hlord2000/nordic-lib-kicad/blocks/nRF54L.kicad_blocks/nRF54L15-CAXX_Reference_Design.kicad_block/nRF54L15-CAXX_Reference_Design.kicad_sch

## KiCad design blocks/nRF54L.kicad_blocks/nRF54L15-CAXX_Reference_Design.kicad_block/nRF54L15-CAXX_Reference_Design.kicad_sch (2026-04-14)

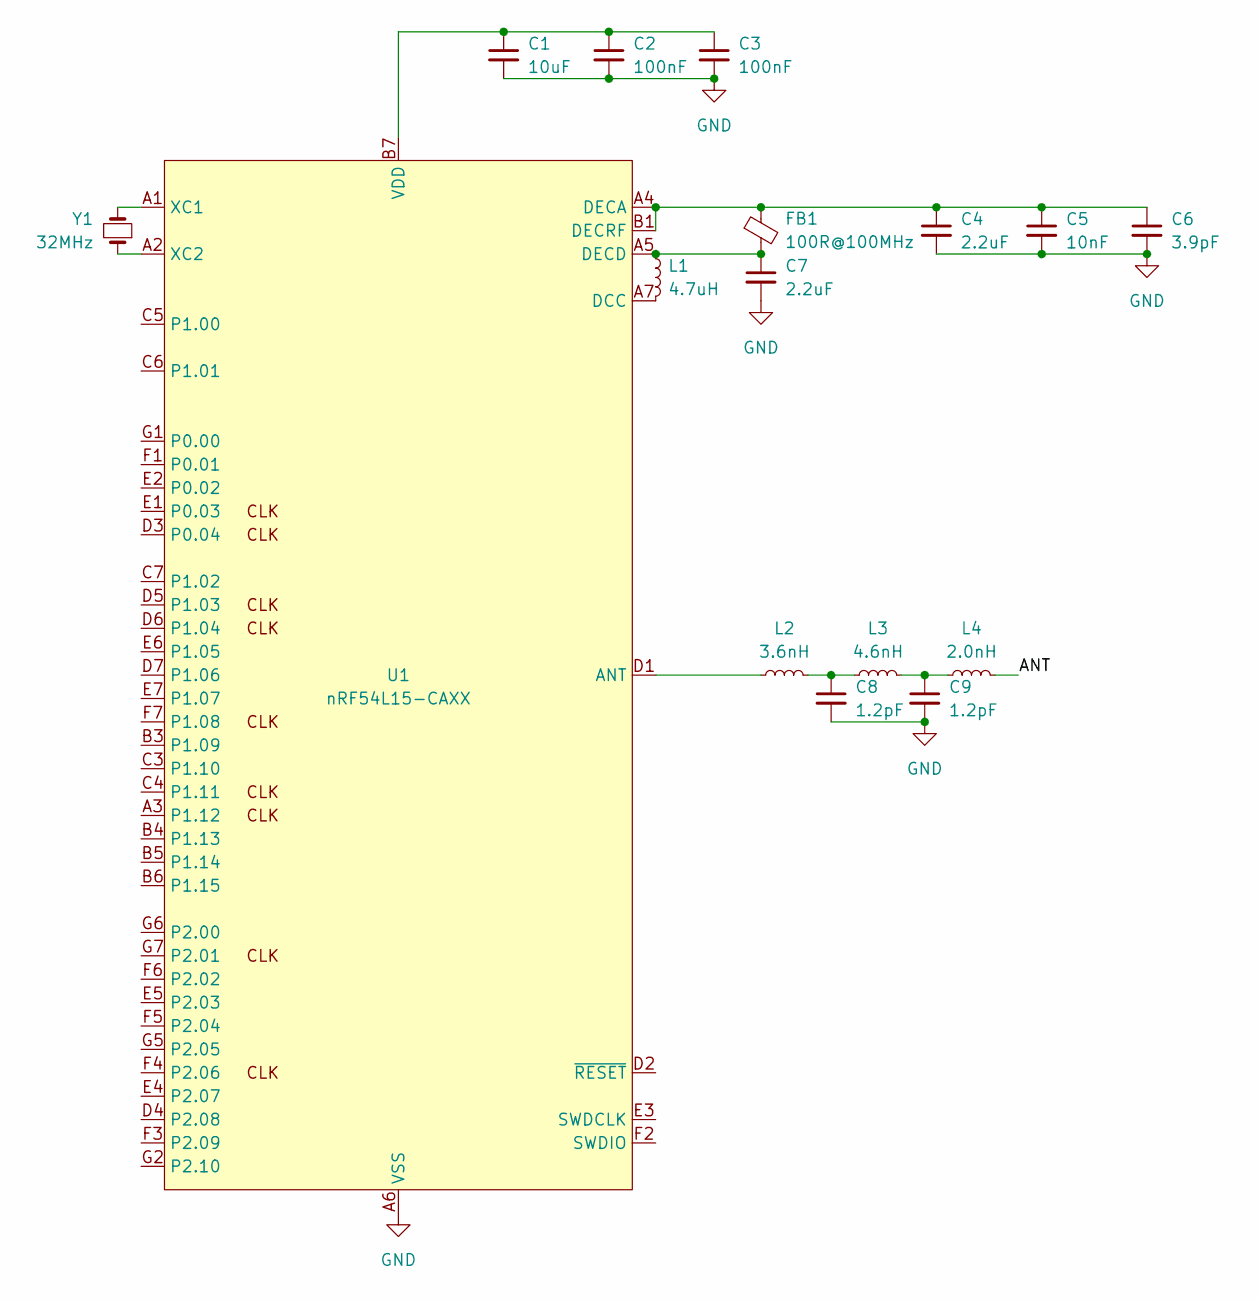
[picture p3: schematic nRF54L15-CAXX_Reference_Design.kicad_sch]

Parts:
C1: 10uF
C2, C3: 100nF
C4, C7: 2.2uF
C5: 10nF
C6: 3.9pF
C8, C9: 1.2pF
FB1: 100R@100MHz
L1: 4.7uH
L2: 3.6nH
L3: 4.6nH
L4: 2.0nH
U1: nRF54L15-CAXX; BGA-47_7x7_2.451x2.245mm
Y1: 32MHz

Connections:
ANT: L4.2
GND: C1.2, C2.2, C3.2, C4.2, C5.2, C6.2, C7.2, C8.2, C9.2, U1.A6 (VSS), U1.C2 (VSS_PA), U1.G4 (VSS)
unnamed: C1.1, C2.1, C3.1, U1.B7 (VDD), U1.G3 (VDD)
unnamed: C4.1, C5.1, C6.1, FB1.1, U1.A4 (DECA), U1.B1 (DECRF)
unnamed: C7.1, FB1.2, L1.1, U1.A5 (DECD)
unnamed: C8.1, L2.2, L3.1
unnamed: C9.1, L3.2, L4.1
unnamed: L1.2, U1.A7 (DCC)
unnamed: L2.1, U1.D1 (ANT)
unnamed: U1.A1 (XC1), Y1.2
unnamed: U1.A2 (XC2), Y1.1
