hlord2000/nordic-lib-kicad/blocks/nRF54L.kicad_blocks/nRF54LM20A-PAXX_Reference_Design.kicad_block/nRF54LM20A-PAXX_Reference_Design.kicad_sch

## KiCad design blocks/nRF54L.kicad_blocks/nRF54LM20A-PAXX_Reference_Design.kicad_block/nRF54LM20A-PAXX_Reference_Design.kicad_sch (2025-09-18)

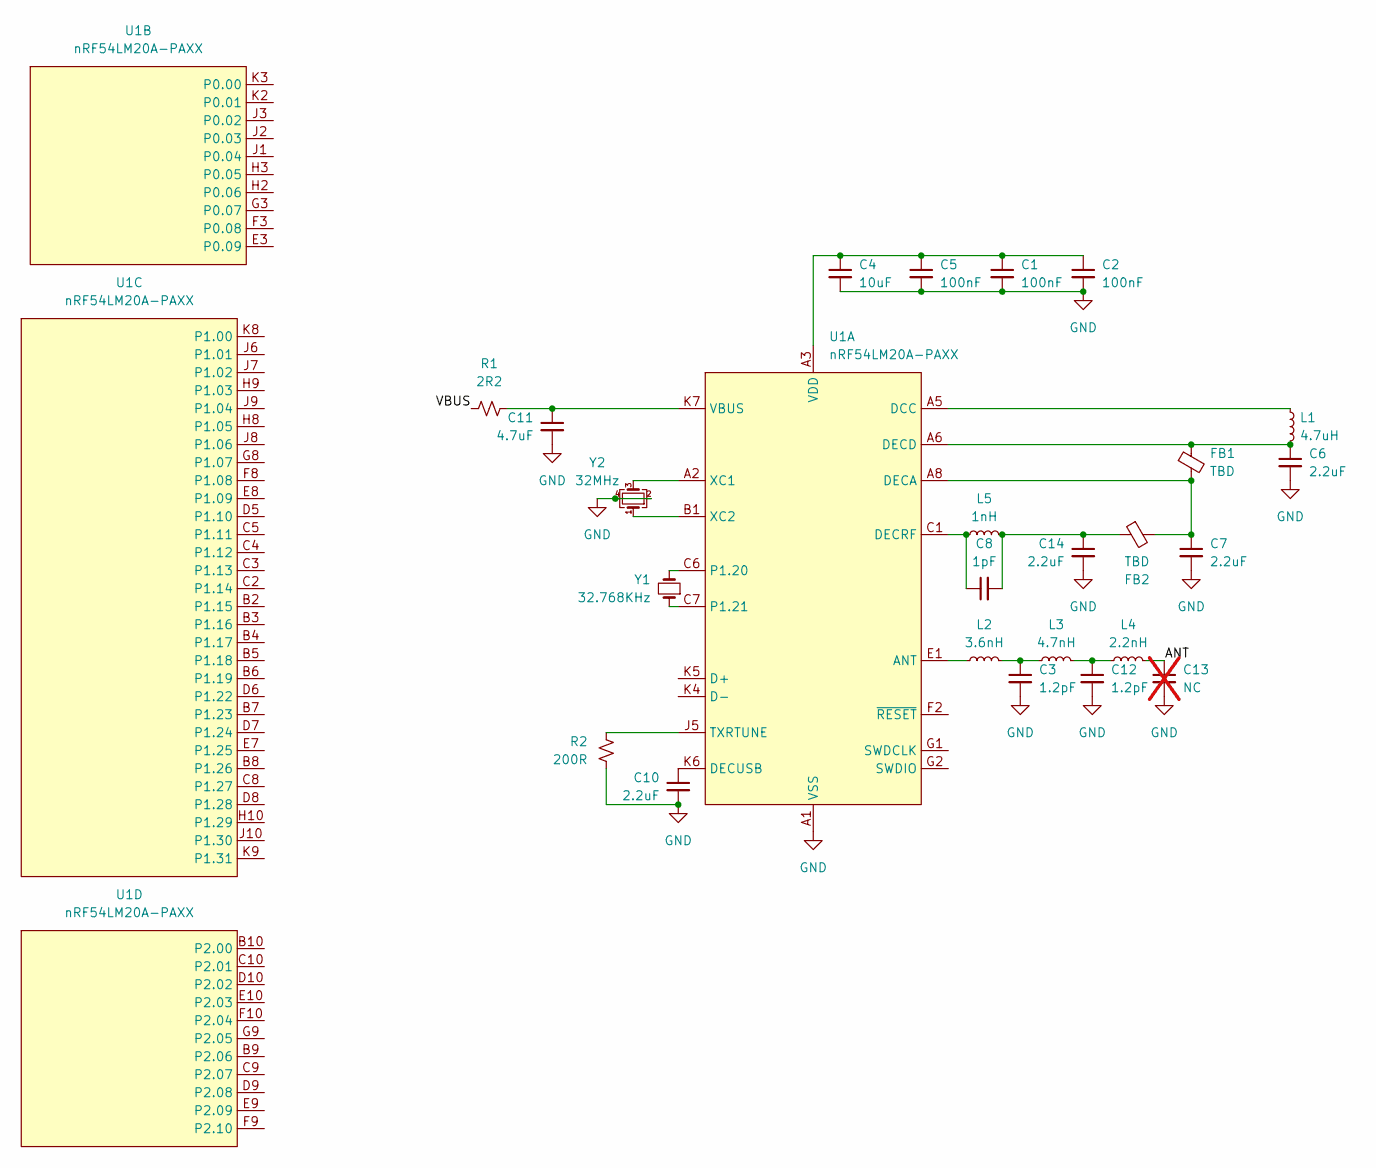
[picture p5: schematic nRF54LM20A-PAXX_Reference_Design.kicad_sch]

Parts:
C1, C2, C5: 100nF; C_0201_0603Metric; LCSC C668346
C3, C12: 1.2pF; C_0201_0603Metric; LCSC C85895
C4: 10uF; C_0402_1005Metric; LCSC C237279
C6, C7, C10, C14: 2.2uF; C_0201_0603Metric; LCSC C76933
C8: 1pF; C_0201_0603Metric; LCSC C85893
C11: 4.7uF; C_0402_1005Metric; LCSC C23733
C13: NC; C_0201_0603Metric; not fitted
FB1, FB2: TBD; L_0201_0603Metric
L1: 4.7uH; L_0603_1608Metric; LCSC C114862
L2: 3.6nH; L_0201_0603Metric; LCSC C89436
L3: 4.7nH; L_0201_0603Metric; LCSC C86126
L4: 2.2nH; L_0201_0603Metric; LCSC C98041
L5: 1nH; L_0201_0603Metric; LCSC C2041448
R1: 2R2; R_0201_0603Metric; LCSC C138154
R2: 200R; R_0201_0603Metric; LCSC C270359
U1: nRF54LM20A-PAXX; Nordic_FCCSP-98_3.67x3.85mm_Layout10x10_P0.35mm_Offcenter
Y1: 32.768KHz; Crystal_SMD_2012-2Pin_2.0x1.2mm; LCSC C99009
Y2: 32MHz; Crystal_SMD_2016-4Pin_2.0x1.6mm; LCSC C2965582

Connections:
ANT: C13.1, L4.2
GND: C1.2, C2.2, C3.2, C4.2, C5.2, C6.2, C7.2, C10.2, C11.2, C12.2, C13.2, C14.2, R2.2, U1.A1 (VSS), U1.A7 (VSS), U1.A10 (VSS), U1.D1 (VSS), U1.D2 (VSS), U1.E5 (VSS), U1.E6 (VSS), U1.F1 (VSS), U1.F5 (VSS), U1.F6 (VSS), U1.K1 (VSS), U1.K10 (VSS), Y2.2, Y2.4
unnamed: C1.1, C2.1, C4.1, C5.1, U1.A3 (VDD), U1.A4 (VDD), U1.A9 (VDD), U1.G10 (VDD), U1.H1 (VDD)
unnamed: C3.1, L2.2, L3.1
unnamed: C6.1, FB1.1, L1.2, U1.A6 (DECD)
unnamed: C7.1, FB1.2, FB2.2, U1.A8 (DECA)
unnamed: C8.1, L5.1, U1.C1 (DECRF)
unnamed: C10.1, U1.K6 (DECUSB)
unnamed: C11.1, R1.2, U1.K7 (VBUS)
unnamed: C12.1, L3.2, L4.1
unnamed: C8.2, C14.1, FB2.1, L5.2
unnamed: L1.1, U1.A5 (DCC)
unnamed: L2.1, U1.E1 (ANT)
unnamed: R2.1, U1.J5 (TXRTUNE)
unnamed: U1.A2 (XC1), Y2.3
unnamed: U1.B1 (XC2), Y2.1
unnamed: U1.C6 (P1.20), Y1.2
unnamed: U1.C7 (P1.21), Y1.1
VBUS: R1.1
